jolleekin/tiu-tracking/Docs/Images/Tag.jpg

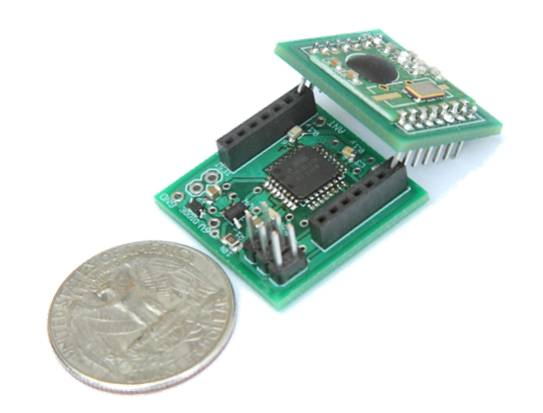
Docs/Images/Tag.jpg
