jolleekin/tiu-tracking/Docs/presentation_outline_v0.1.odp

## TIU Tracking

Dung Le

Lynh Pham

Tri Truong

Man Hoang

Daniel Ferguson

## Introduction

- What we were given
- What we came up with
- Power
- Size
- Accuracy

## Agenda

- Hardware
- Firmware
- Software
- Deployment
- Results
- Conclusion

## Hardware Overview

- Components
  - RF12
  - Atmega
  - Wifly
- Devices
  - Detector
  - Tag
  - Proxy

## Detector Hardware

## Tag Hardware

## Proxy Hardware

## Agenda

- Hardware
- Firmware
- Software
- Deployment
- Results
- Conclusion

## Firmware Overview

## Detector & Proxy Firmware

## Tag Firmware

## Agenda

- Hardware
- Firmware
- Software
- Deployment
- Results
- Conclusion

## Software Overview

## Controller

## Locating Algorithm

## Web Application

## Agenda

- Hardware
- Firmware
- Software
- Deployment
- Results
- Conclusion

## Deployment Overview

- Detector
- Tag
- Proxy
- Web App
- Controller

## Detector Deployment

- What needs to be done to a detector before placement?

## Tag Deployment

- What needs to be done to a tag before you fix it to a TIU?

## Proxy Deployment

- Where do you place the Proxy?
- Why?

## Web App

- What is the web apps role in deployment?

## Controller

- What is the controllers role in deployment?

## Agenda

- Hardware
- Firmware
- Software
- Deployment
- Results
- Conclusion

## Results

- Power

## Results

- Size

## Results

- Accuracy

## Agenda

- Hardware
- Firmware
- Software
- Deployment
- Results
- Conclusion

## Conclusion

- Suggestions for moving forward
- What we could have done better
- What we did well
- What we learned
