jolleekin/tiu-tracking/Docs/Images/General_Diagram.pptx

Back-end

Front-end


Users


Web App

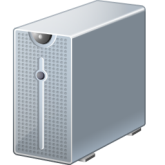
[picture p137: figure]

Database


Admin

Detector


Tag

Controller


Proxy

Wi-Fi

Location Engine
