jolleekin/tiu-tracking/Docs/TIU_Tracking_Poster_v8.pptx

TIU Tracking System

Capstone 2011
Sponsored by Intel
Advisor: Prof. Robert Daasch

Team Members:
Daniel Ferguson – Dung Le
Lynh Pham – Man Hoang – Tri Truong


Introduction

Intel's large and complex validation labs contain many Testing Interface Unit's(TIU) used in validating hardware. A TIU is a custom PCB that provides test points that a testing machine can probe. Since the hardware to be tested is varied, there exists a variety of different TIU's, and as such, finding a particular TIU is useful because, previously, the testing machine had to be broken down to identify the TIU it was using. The guiding requirements are that the system must be small, inexpensive, and low power.

Approach

Our system uses an RF transceiver mesh network to track mobile assets indoors. The system determines an asset’s current location by matching the RF fingerprint, based on signal strength, of a Tags periodic broadcasts with previously collected fingerprints stored in a database.
Why RF signal strength?
Radio Received Signal Strength Indication (RSSI) is a measurement of the amount of power received by antenna. Theoretically, distances can be approximated based on the relationship between transmitted and received signal strength.
We based our system on RF signal strength because alternative choices such as GPS, IR, and Acoustics either cannot work indoors, or requires line of sight. Also, low power RF transceivers are readily available.
For scalability, a mesh network of detectors relay all data to a centralized controller where locations of tags are calculated and saved in a database. An easy to use web application provides visualization of tag locations, as well as other maintenance details.

Back-end


Web App

Controller

Front-end


Users


Admin


Database


Tag

Wi-Fi


Proxy

Detector

Detector

Design

Front End Network
Tags
- Attached to TIUs.
- Periodically broadcast.
- When not broadcasting, in a low power state.
Detectors
- Determine RSSI of broadcasting tags.
- Must always be listening for a tag to broadcast.
- Rebroadcasts the message, which results in messages always propagating toward the proxy.
- Messages are relayed to the proxy via a controlled flooding mechanism.
- Collision avoidance is achieved using time division.
Wi-Fi Proxy
- Receives data from the mesh network and relays data to the controller.

Products


Detector
- Size: 3.5”x1”
- ATMega328p MCU
- RF12B transceiver at 434MHz
- 9V battery/adapter
- Cost

Asset Tag
- Size: 1”x1”x1”
- ATMega328p MCU
- RF12B transceiver at 434MHz
- 20mm coin cell battery
- Battery life: 3 months
- Cost

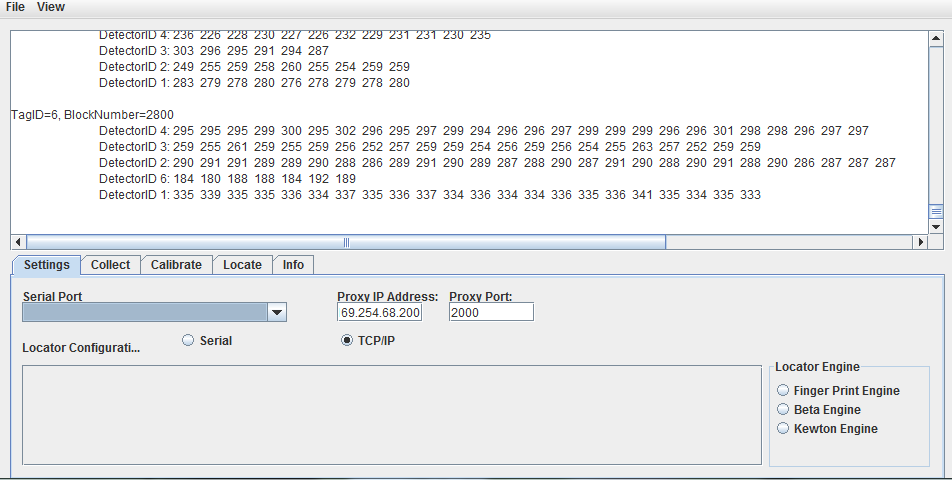
[picture p138: figure]

Back-end Network
Controller
- Primary link between the mesh network and the back end infrastructure
- Communicates with mesh network
- Executes the locating algorithm
- Communicates with the Database
Fingerprint Algorithm
- A progressively constrained, nearest neighbor algorithm, using Euclidean distance as the matching metric.
- Heuristics, input and output filters are employed that further enhance the accuracy and reliability of the locating process
Web Application
- Primary user interface with Interactive 2D map
- Search TIU and detector via ID
- Show battery level of all elements in the mesh network
- Configure tag and detector
- Configure geometry of tracking area
SQL Database
- Stores locations and battery information of all tags and detectors
- Stores user accounts

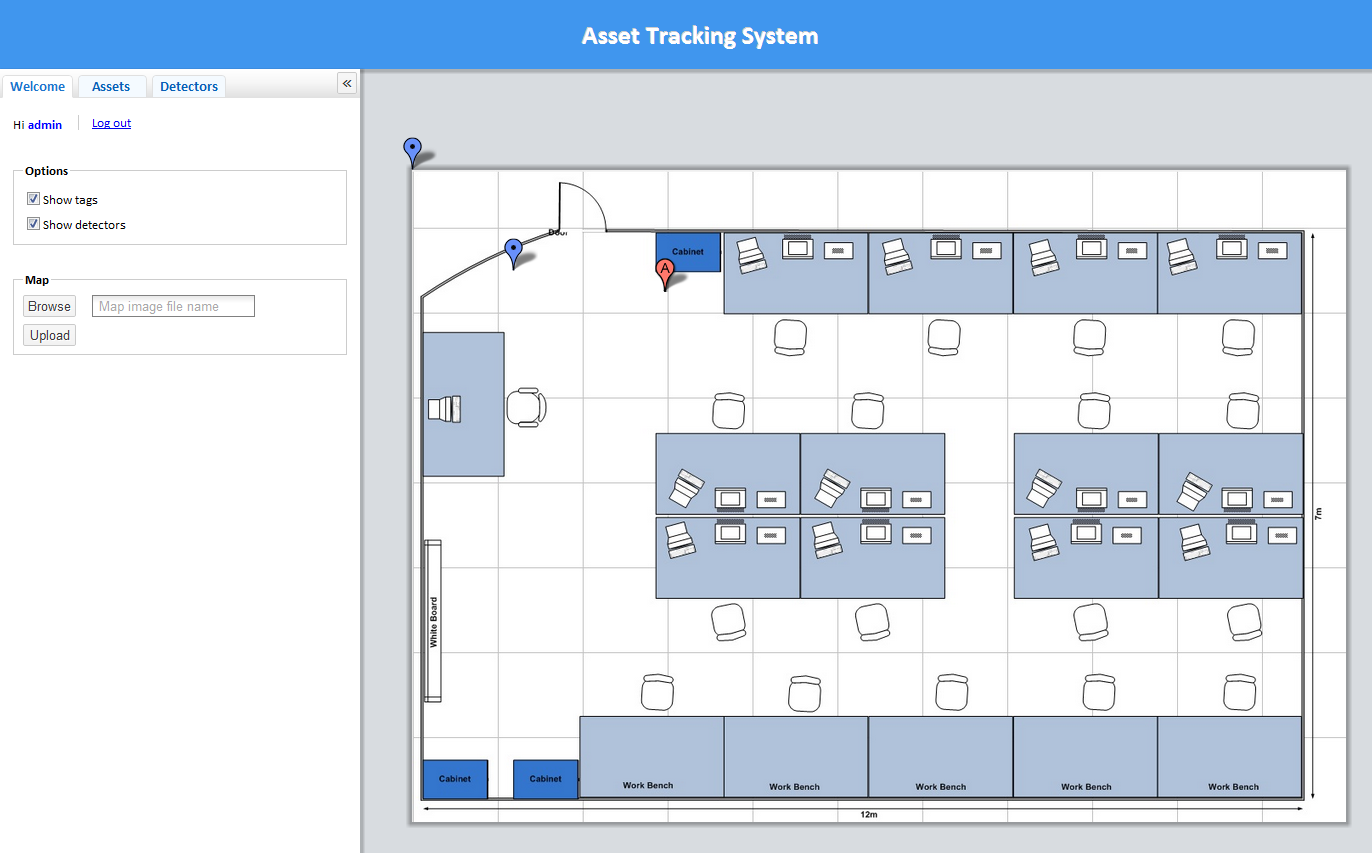
[picture p139: figure]

Test Results

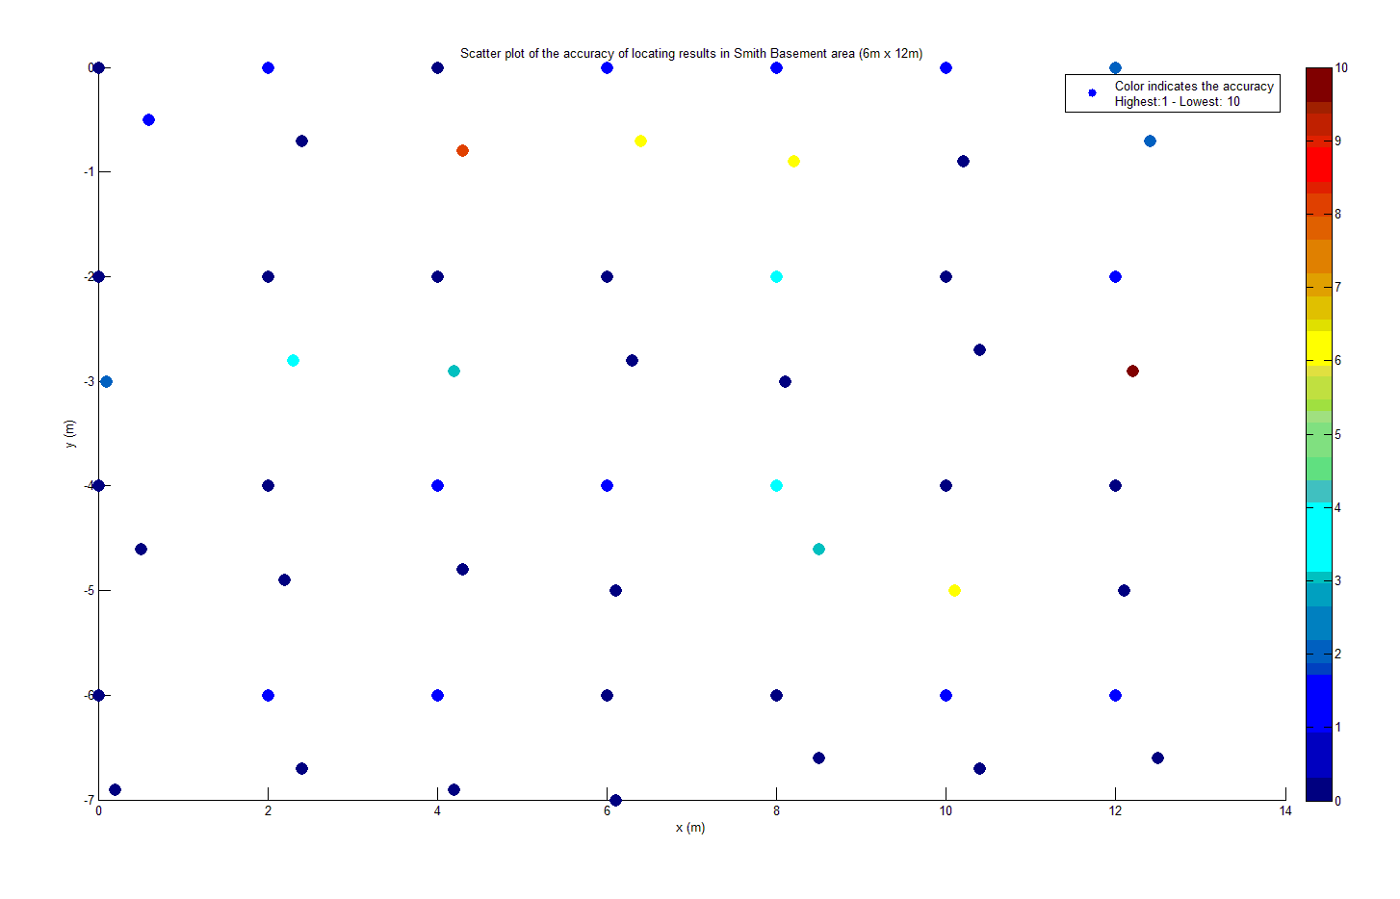
[picture p140: figure]

where
  - d is the Euclidean distance between calibrated RSSI vectors and located RSSI vector.
  - Sci is RSSI value received by detector i in calibrating phase
  - Sli is RSSI value received by detector i in locating phase
  - N is the number of detectors participating into the locating phase

Conclusions

Accomplish , contribution
The accuracy of the tracking system needs to be enhanced by considering antenna design and advanced locating algorithm. Noise filter can be implemented on both hardware and software to achieve desired performance.

Department of Electrical and Computer Engineering
