jolleekin/tiu-tracking/Docs/TIU_Tracking_Poster_v4.pptx

TIU TRACKING SYSTEM


Capstone Project 2011
Advisor: Prof. Robert Daasch
Sponsored by Intel

Team members:
Lynh Pham – Daniel Ferguson
Dung Le – Man Hoang – Tri Truong


Introduction

This system uses an RF transceiver network to track mobile assets indoors, where more obvious solutions, such as GPS, are unable to function. The system determines an asset’s current location by matching the RF fingerprint of its periodic broadcasts with previously collected fingerprints stored in a database.

Requirements

- Asset tag’s size: 1” x 1” x 1”
- Low power consumption
- Accurate
- Web application as user
- interface
- 2D map display
- Scalable tracking area
- Low cost solution

Approach

This system uses an RF transceiver network to track mobile assets indoors, where more obvious solutions, such as GPS, are unable to function. The system determines an asset’s current location by matching the RF fingerprint of its periodic broadcasts with previously collected fingerprints stored in a database.

Indoor tracking area

Design

This system uses an RF transceiver network to track mobile assets indoors, where more obvious solutions, such as GPS, are unable to function. The system determines an asset’s current location by matching the RF fingerprint of its periodic broadcasts with previously collected fingerprints stored in a database.

Features

RF Mesh Network
- User and Admin interface
- Interactive 2D map
- Search TIU and detector via ID
- Show battery level
- Add and remove tag/detector
- Change geometry of tracking area

Wi-Fi Proxy
- WiFly 802.11b/g at 2.4GHz
- RF12B transceiver at 434MHz
- MCU ATMega328p
- Use 9V battery/adaptor

Products

Test Results

Conclusions

The accuracy of the tracking system needs to be enhanced by considering antenna design and advanced locating algorithm. Noise filter can be implemented on both hardware and software to achieve desired performance.


Asset Tag
- Size: 1”x1”x1”
- Use RF12B transceiver at 434MHz
- Use MCU ATMega328p
- Use coin cell 20mm battery
- Battery life: more than 1 month

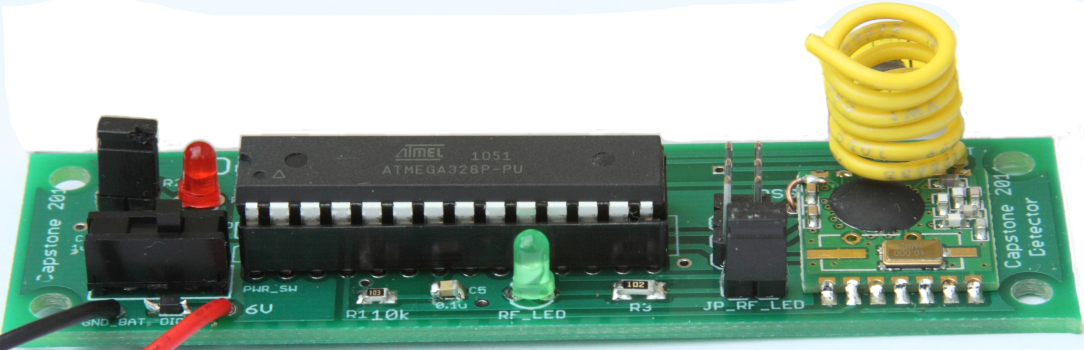
[picture p141: figure]

Detector
- Size: 3.5”x1”
- Use RF12B transceiver at
434MHz
- Use MCU ATMega328p
- Use 9V battery/adapter

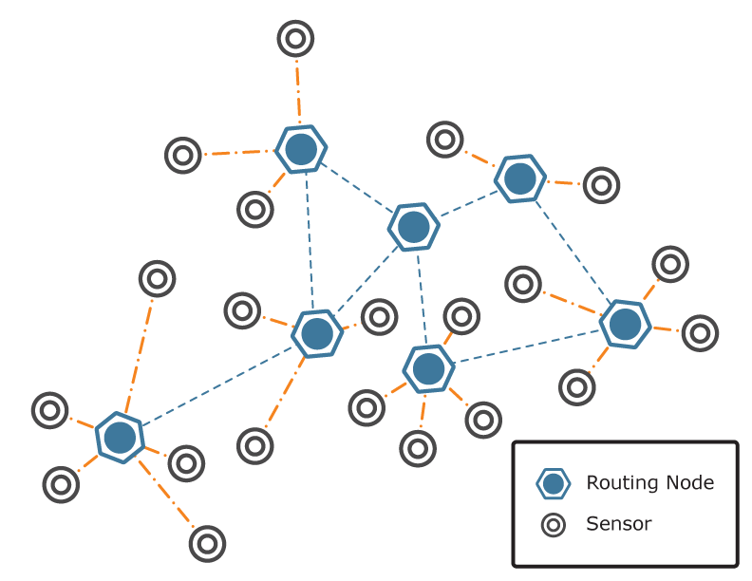
[picture p142: figure]

Mesh Network Concept

Controller
- Provide utilities to set up the system
- Written in Java
- Cross platform
- Easy to use
- Process data and calculate assets’ location


Web Application
- User and Admin interface
- Interactive 2D map
- Search TIU and detector via ID
- Show battery level
- Add and remove tag/detector
- Change geometry of tracking area

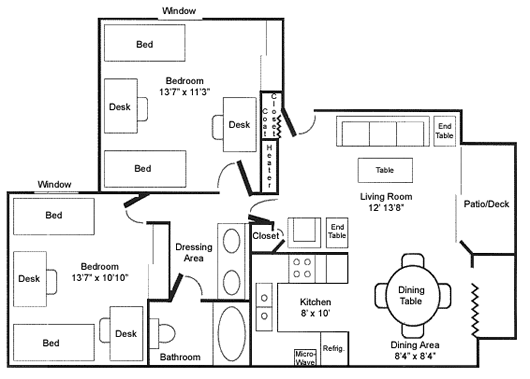
[picture p143: figure]

Fingerprint Algorithm
- Calibrate and create a database of signal signature.
- Locate by matching signal pattern
- Interpolate calculated results

SQL Database
- RSSI-distance model or RF fingerprinting
- Location update interval
- Geometry of the tracking area
- Identifications, locations, and battery levels of the TIUs

Department of Electrical and Computer Engineering
