jolleekin/tiu-tracking/Docs/TIU_Tracking_Poster_v1.pptx

TIU TRACKING SYSTEM

METHODS & APPROACH

Capstone 2011

RESULTS

Asset Tag
- Size: 1”x1”x1”
- Use RF12B transceiver with 434MHz
- Use MCU ATMega328p
- Use coin cell 20mm battery
- Battery life: more than 1 month

Proxy
- Use WiFly 802.11b/g with 2.4GHz
- Use RF12B transceiver with 434MHz
- Use MCU ATMega328p
- Use 9V battery/adaptor


ABSTRACT

This system uses an RF transceiver network to track mobile assets indoors, where more obvious solutions, such as GPS, are unable to function. The system determines an assets current location by matching the RF fingerprint of its periodic broadcasts with previously collected fingerprints stored in a database

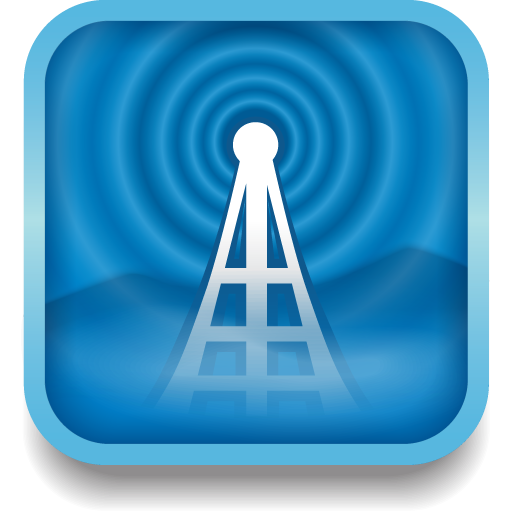
[picture p144: figure]

Locating Algorithm

- Finger-Print
- Voting Method

Back-end

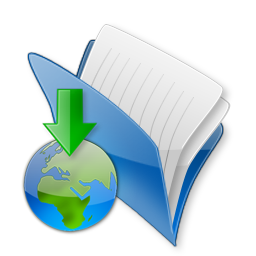
[picture p145: figure]

User Interface

- Web Application
- User Interface
- Admin Interface

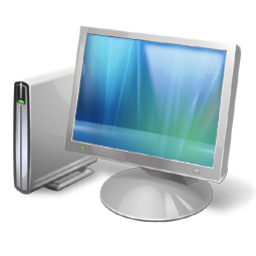
[picture p146: figure]

Data Management

- Controller
- SQL Database
- Tracking Area
- Battery Level

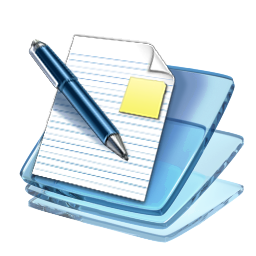
[picture p147: figure]

Detector
- Size: 3.5”x1”
- Use RF12B transceiver with
434MHz
- Use MCU ATMega328p
- Use 9V battery/adapter

Controller
- Daniel part
- …………………..

Web Application
- User and Admin interface
- Interactive 2D map
- Search TIU and detector via ID
- Show battery level
- Add and remove tag/detector
- Change geometry of tracking area

SQL Database
- RSSI-distance model or RF fingerprinting
- Location update interval
- Geometry of the tracking area
- Identifications, locations, and battery levels of the TIUs


Infrastructure

- RF Transceiver
- Mesh Network
- Wi-Fi Proxy
- Server Computer

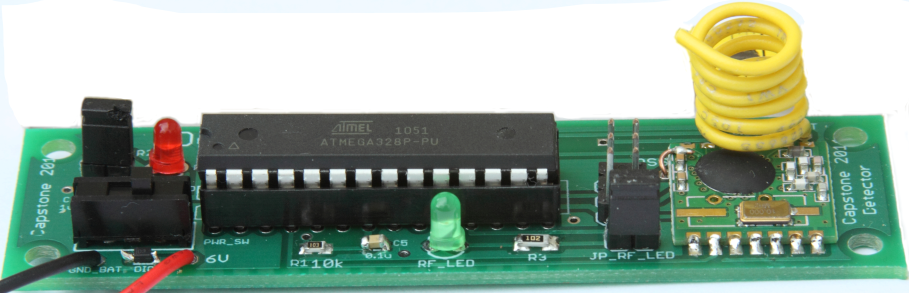
[picture p148: figure]

TIU Tracking System

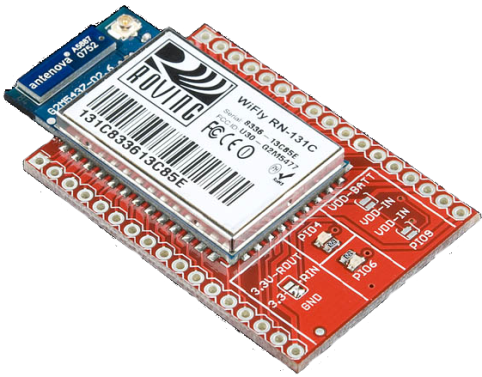
[picture p149: figure]

REQUIREMENTS

- Asset tag’s size: 1” x 1” x 1”
- Low power consumption
- High accuracy
- Web application as user
interface
- 2D map display
- Scalable tracking area
- Low cost solution


Admin


Internet


Users


Detector

Front-end

Detector

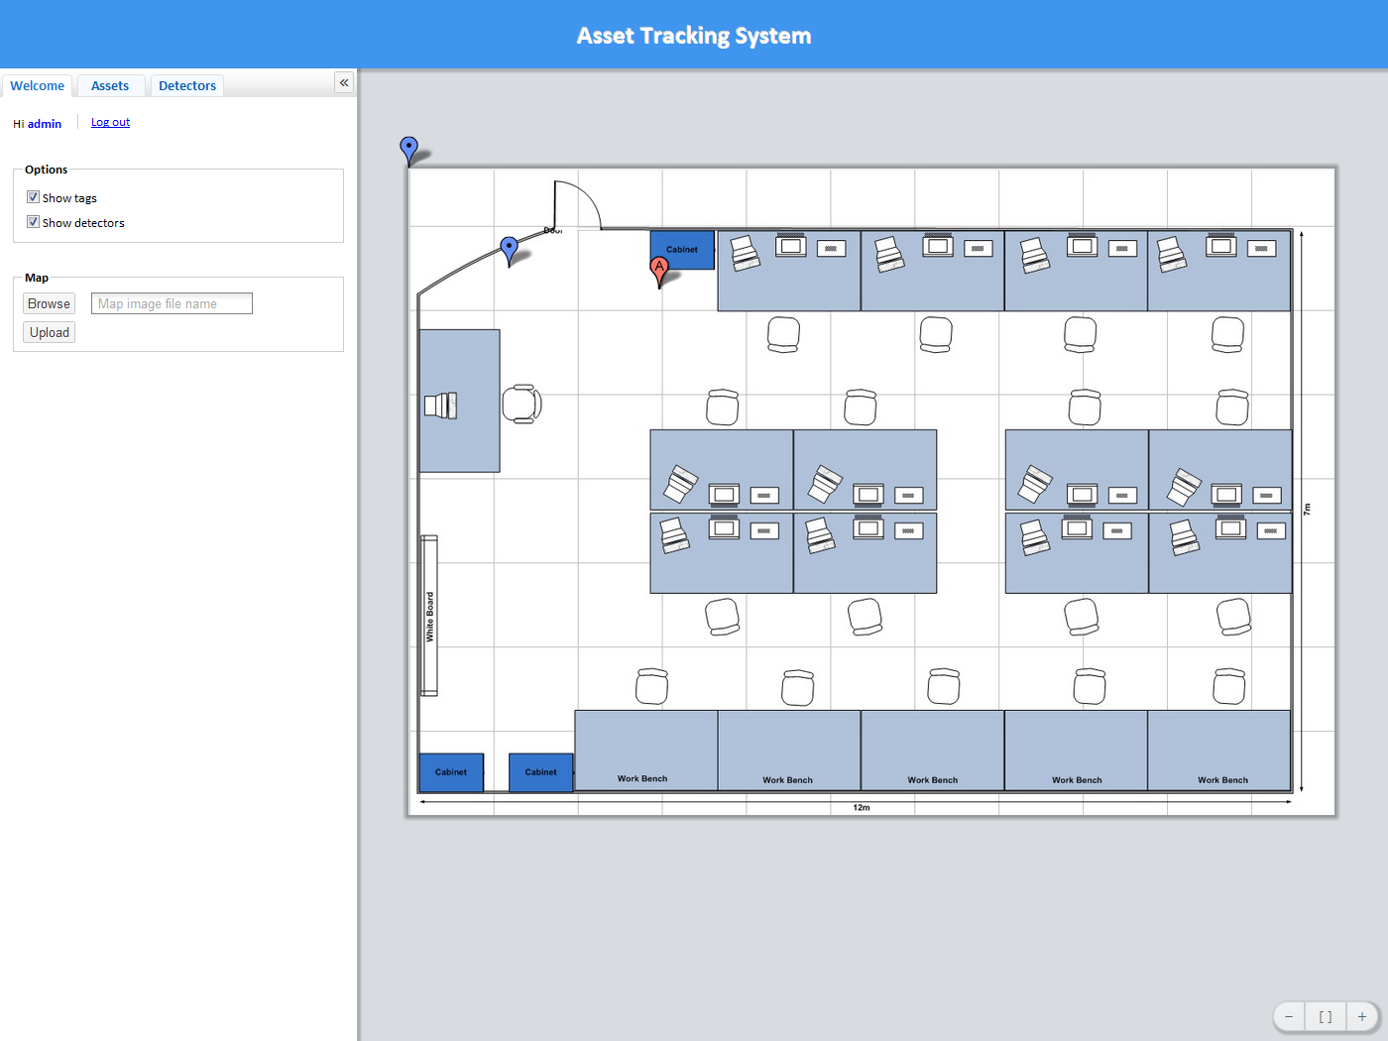
[picture p150: figure]

Controller


Proxy

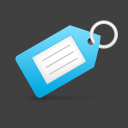
[picture p151: figure]

Tag

Detector


- Capacity of lithium coin cell: 240mAh
- Transmission time: 3ms every 1 seconds
- Active current: 30mA (RF transceiver + MCU)
- Sleep current: 0.0425mA

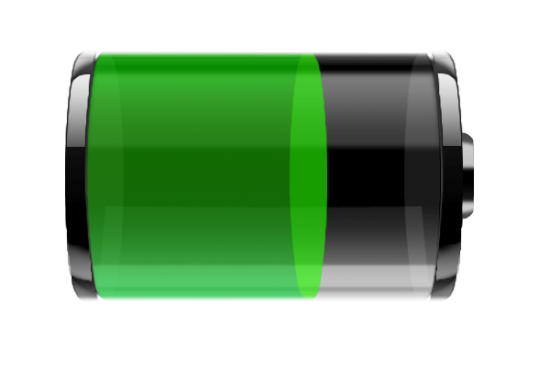
[picture p152: figure]

Battery Life

- Testing ………

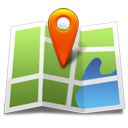
[picture p153: figure]

Accuracy

CAPSTONE TEAM

Sponsor: Intel
Advisor: Prof. Robert Daasch
Members: Dung Le
Tri Truong
Lynh Pham
Man Hoang
Daniel Ferguson

Advantages

- Small size
- Low power consumption
- Easy scalability
- Low cost

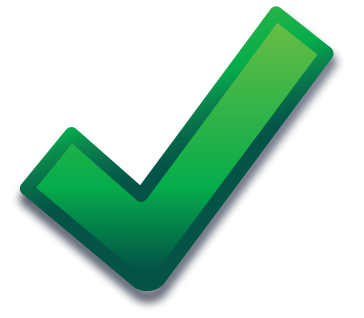
[picture p154: figure]

Disadvantages

- Noise sensitive
- Calibration required

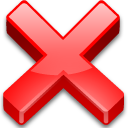
[picture p155: figure]

CONCLUSIONS

The tracking system consists of two primary parts: hardware and software. The hardware infrastructure is built upon RF technology. The number of detectors will be scaled in order to achieve the desired accuracy and efficiency..
……………………………….

Department of Electrical and Computer Engineering
