jolleekin/tiu-tracking/Docs/Detector_2.JPG

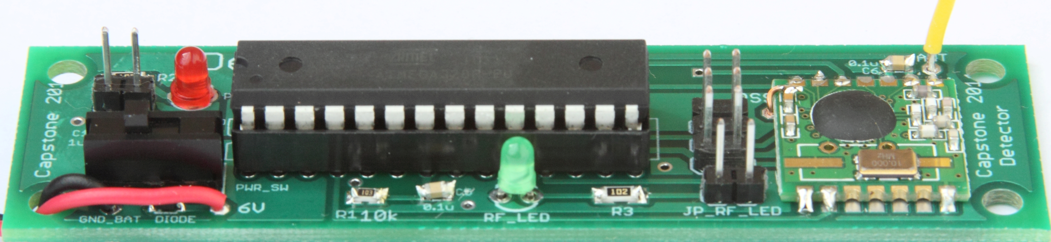
Docs/Detector_2.JPG
