jolleekin/tiu-tracking/Docs/Detector_3.JPG

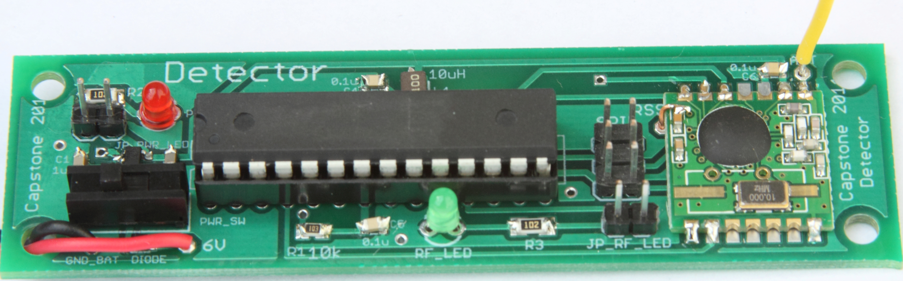
Docs/Detector_3.JPG
