jolleekin/tiu-tracking/Docs/Images/328PQFP.jpg

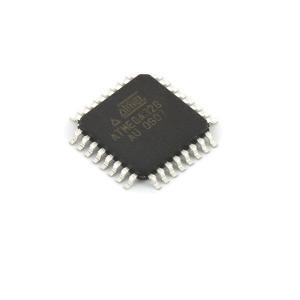
Docs/Images/328PQFP.jpg
