jolleekin/tiu-tracking/Docs/Images/CPC-BestOverall2011_02.png

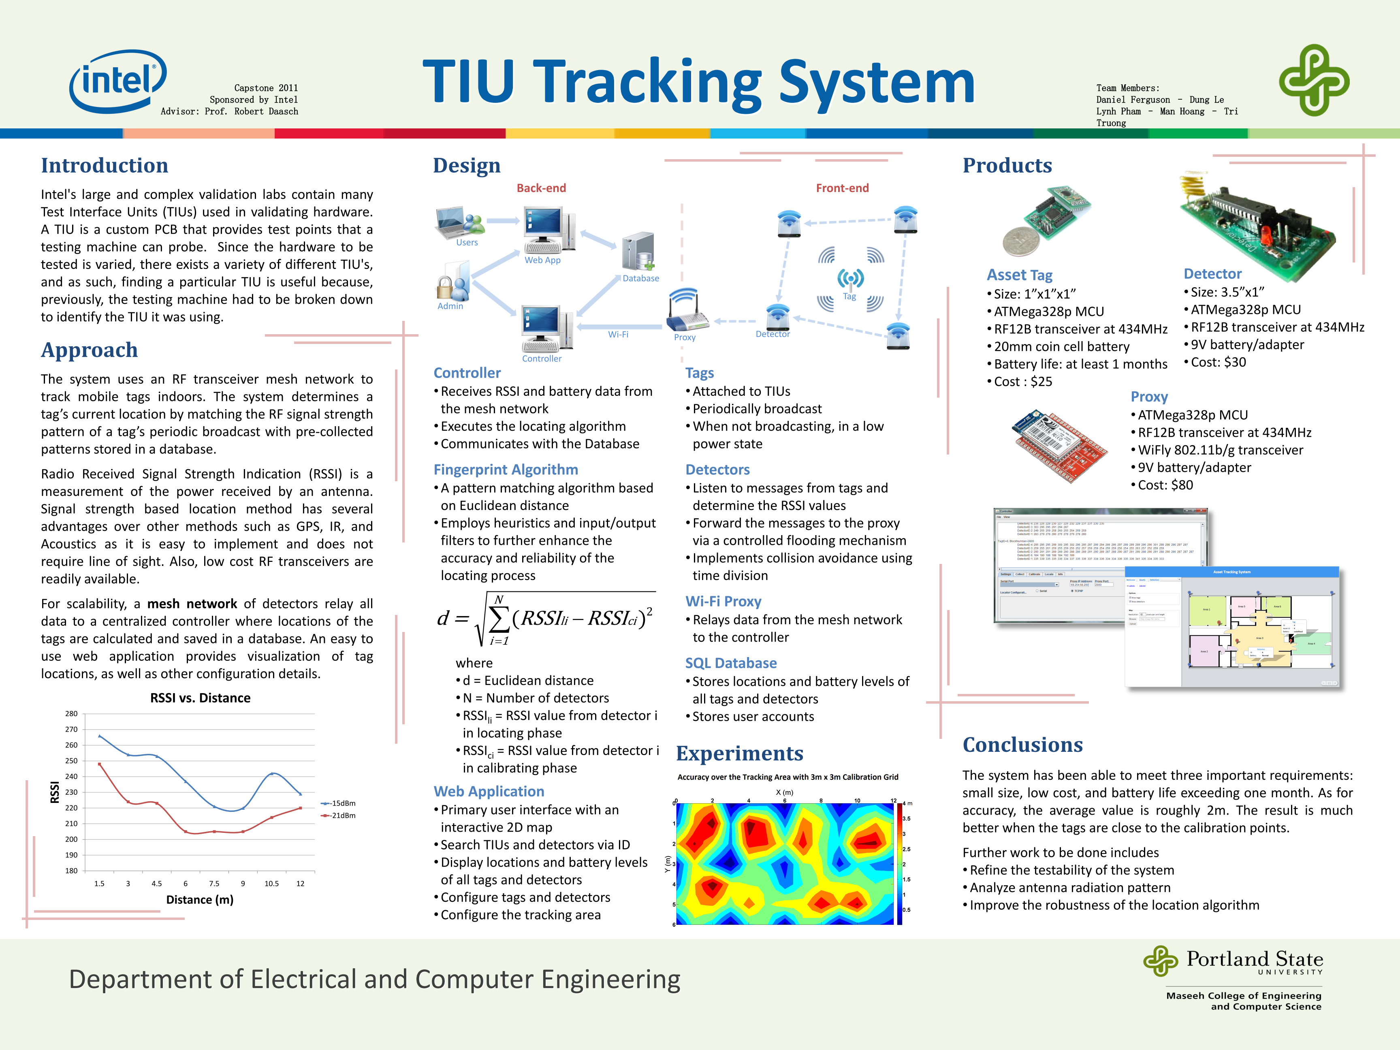
Docs/Images/CPC-BestOverall2011_02.png
