jolleekin/tiu-tracking/Docs/Images/detector_schem.png

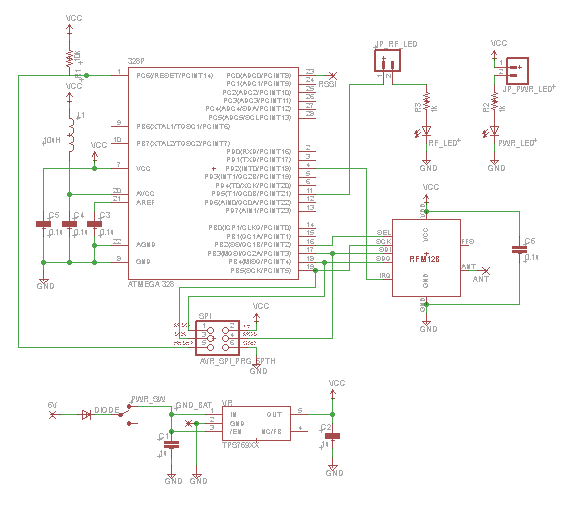
Docs/Images/detector_schem.png
