jolleekin/tiu-tracking/Docs/Images/mesh_modified.gif

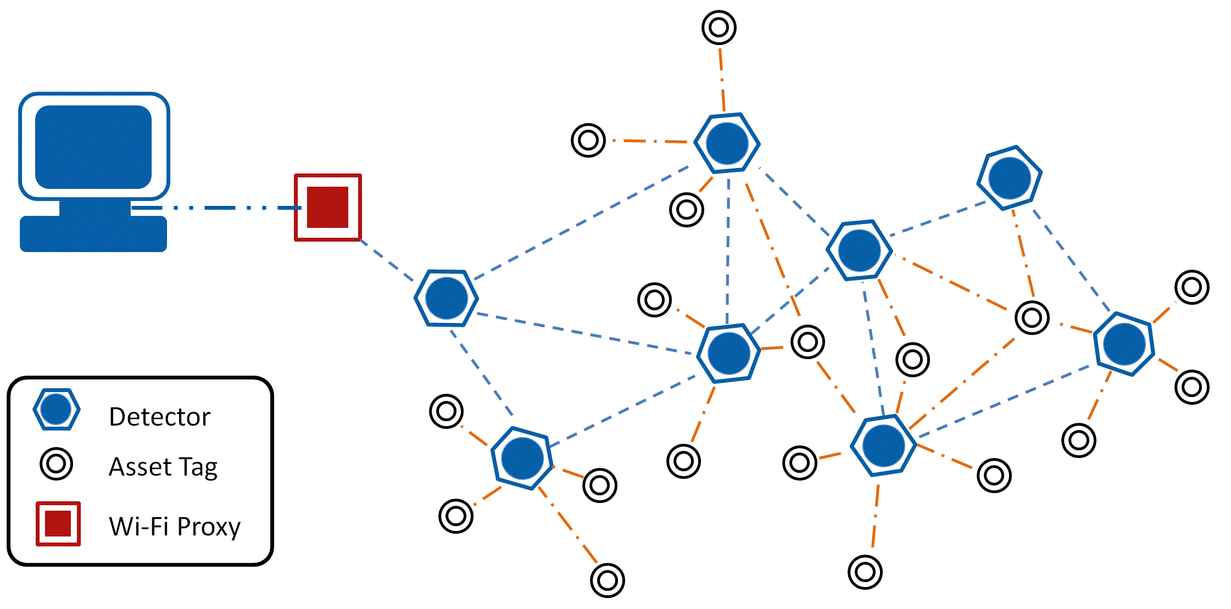
Docs/Images/mesh_modified.gif
