jolleekin/tiu-tracking/Docs/TAG_1.JPG

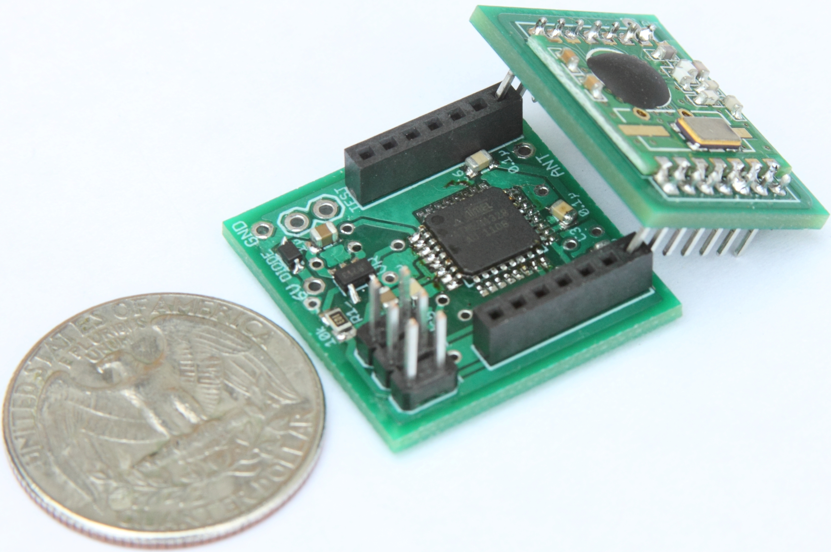
Docs/TAG_1.JPG
