jolleekin/tiu-tracking/Docs/TAG_2.JPG

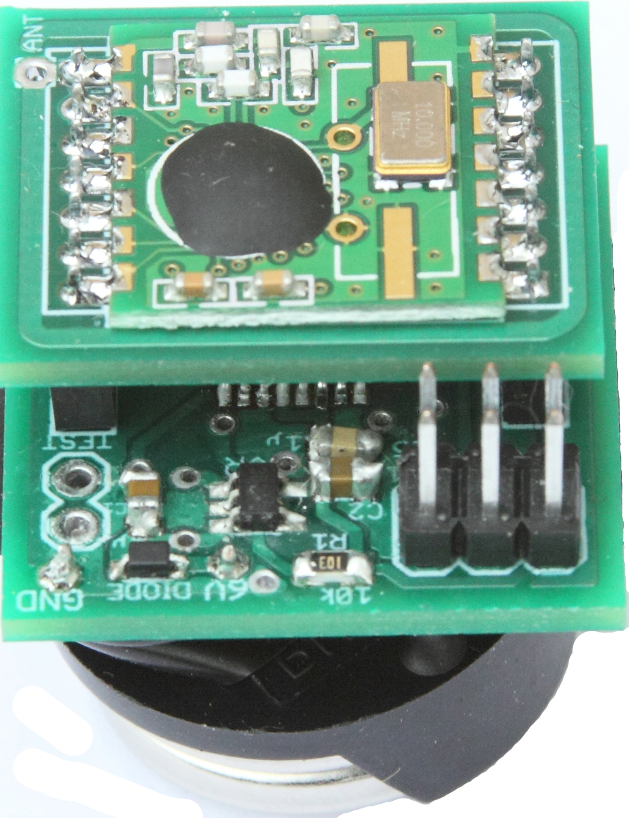
Docs/TAG_2.JPG
