jolleekin/tiu-tracking/Docs/TAG_3.JPG

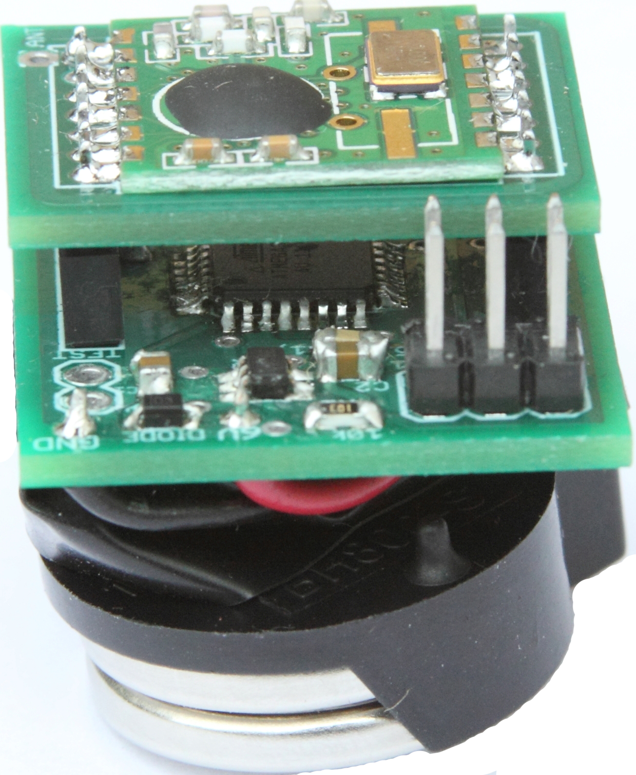
Docs/TAG_3.JPG
