jolleekin/tiu-tracking/Software/WebApp/images/BoxShadow.png

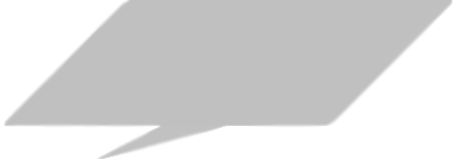
Software/WebApp/images/BoxShadow.png
