jolleekin/tiu-tracking/Software/WebApp/images/FloorPlan.jpg

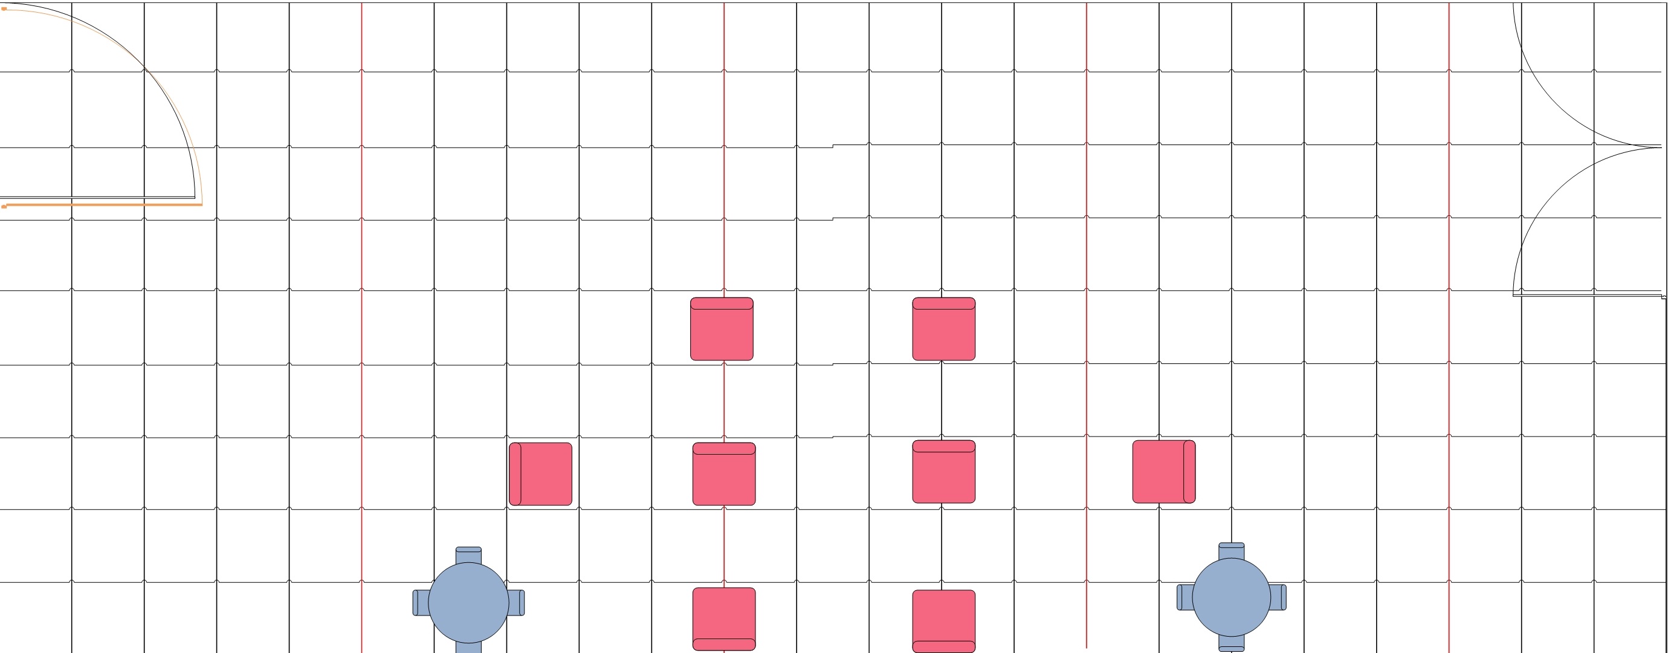
Software/WebApp/images/FloorPlan.jpg
