jolleekin/tiu-tracking/Software/WebApp/images/WaterColor.jpg

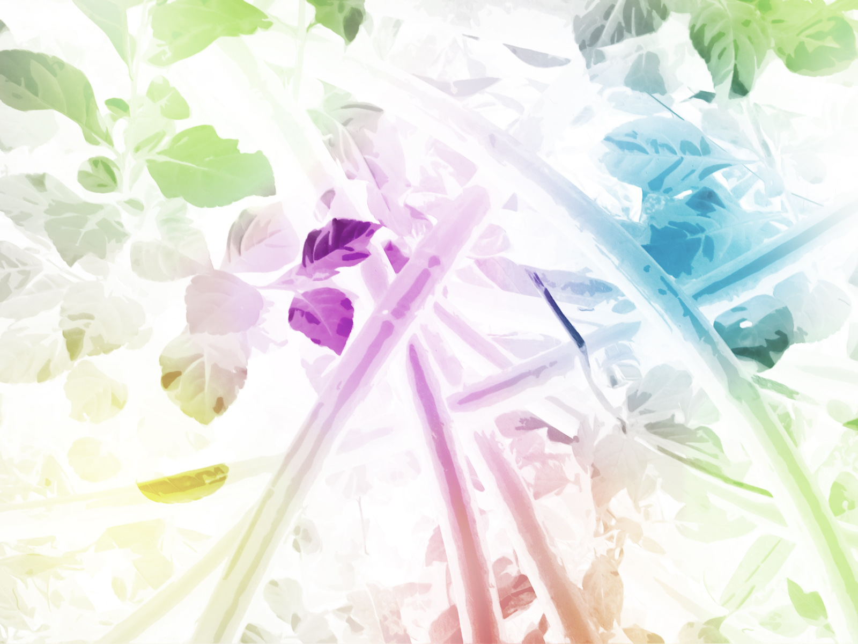
Software/WebApp/images/WaterColor.jpg
